eshazen/scope-clock/Data/3BP1 Base 1.gif

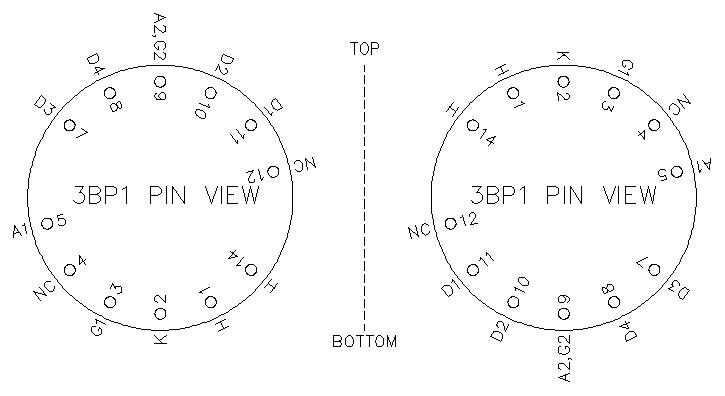
Data/3BP1 Base 1.gif
