eshazen/scope-clock/Data/3BP1 CRT 2.gif

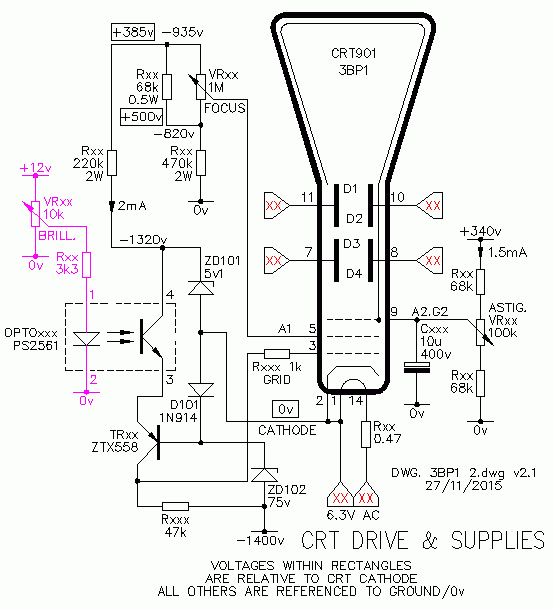
Data/3BP1 CRT 2.gif
