eshazen/scope-clock/Data/3BP1 NBTV Initial 9.gif

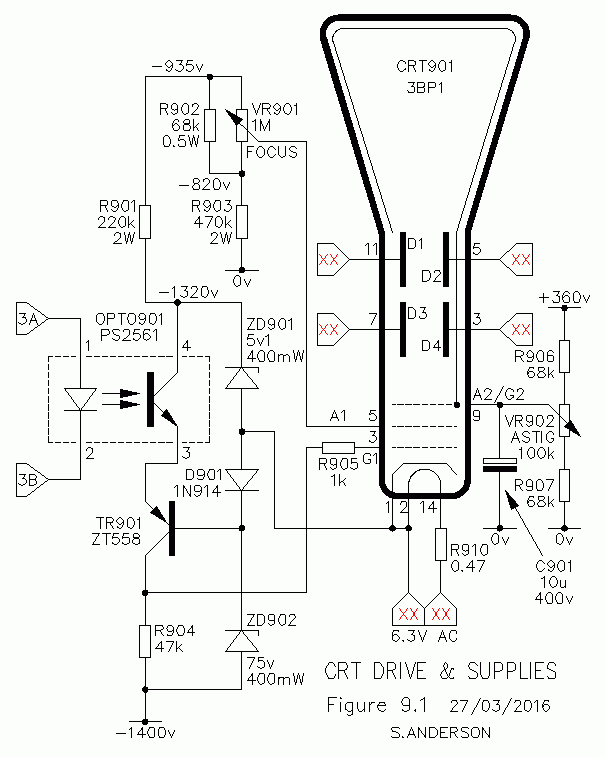
Data/3BP1 NBTV Initial 9.gif
