eshazen/scope-clock/Data/3BP1 PSU 2.gif

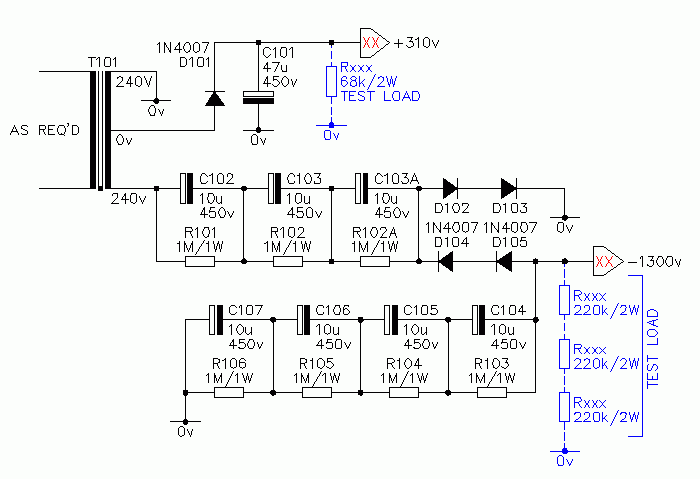
Data/3BP1 PSU 2.gif
