eshazen/scope-clock/Data/3BP1 PSU 3.gif

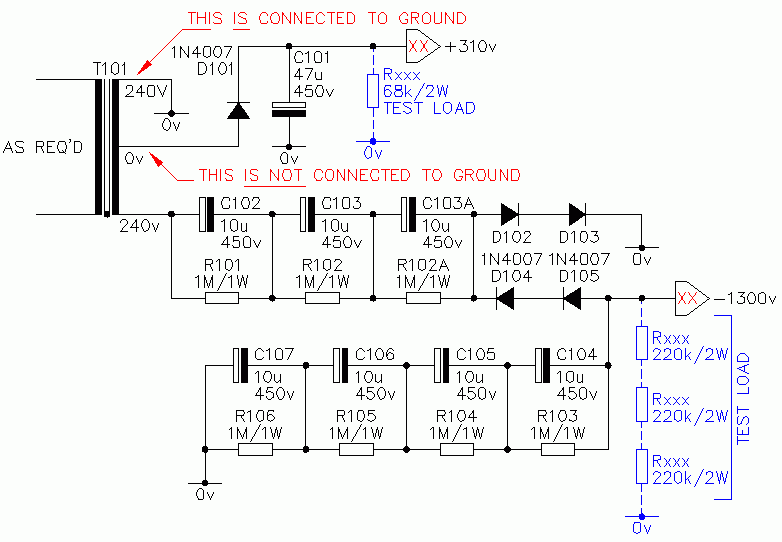
Data/3BP1 PSU 3.gif
