eshazen/scope-clock/Data/3BP1 PSU 4.gif

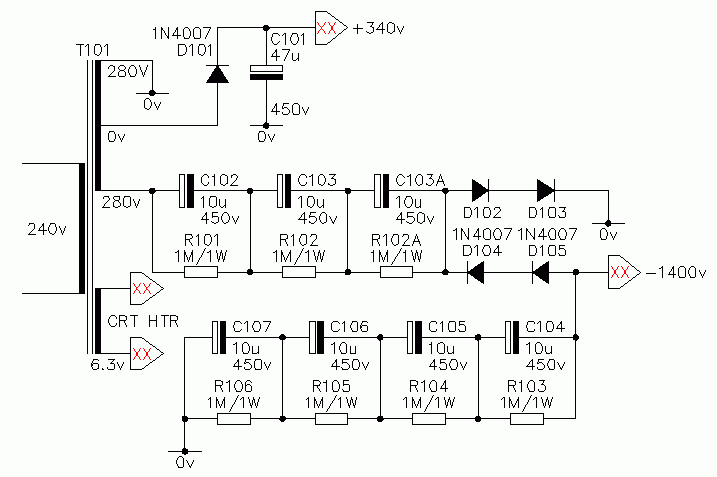
Data/3BP1 PSU 4.gif
