eshazen/scope-clock/Data/44a.gif

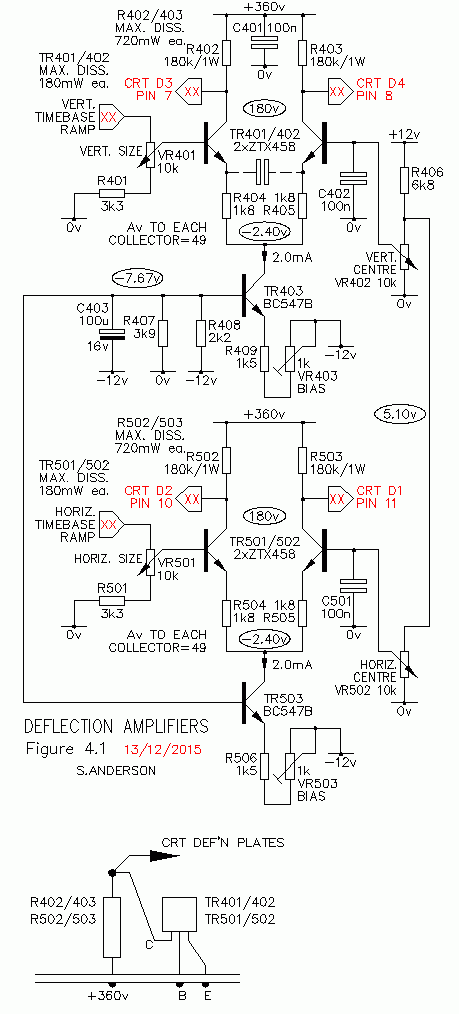
Data/44a.gif
