eshazen/scope-clock/hardware/psu/3D/e_0100.2041d007.step

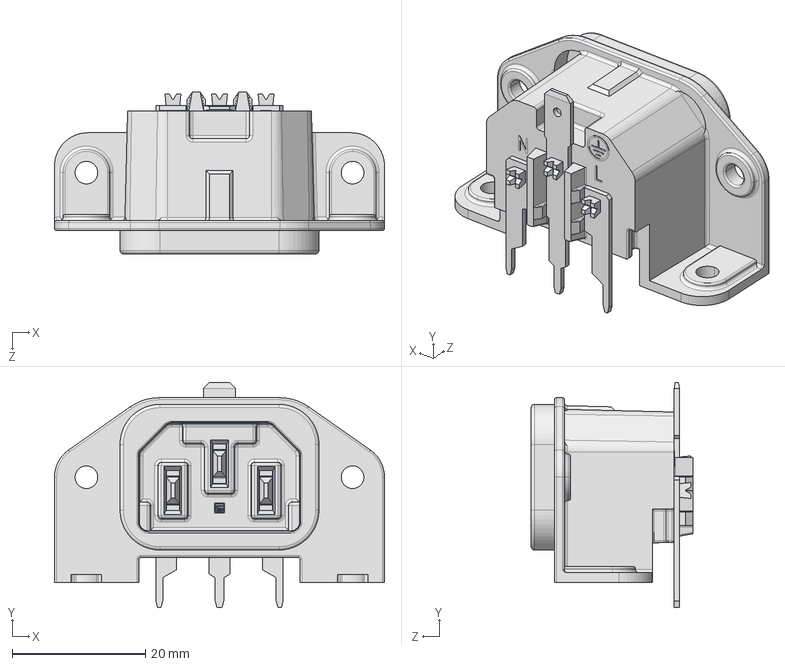
[picture p38: CAD file, 2022-12-22]
hardware/psu/3D/e_0100.2041d007.step
49.6 x 33.9 x 24.3 mm
