eshazen/scope-clock/hardware/case/back.dxf

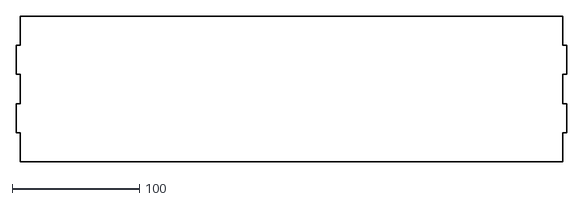
[picture p39: CAD file, 2024-02-05]
hardware/case/back.dxf
431.8 x 114.3
