eshazen/scope-clock/hardware/psu/3D/fuse_holder-Group001.step

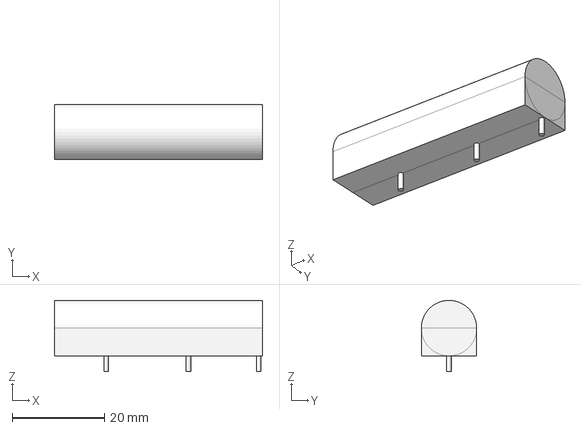
[picture p40: CAD file, 2022-12-22]
hardware/psu/3D/fuse_holder-Group001.step
45.0 x 12.0 x 15.4 mm
