eshazen/scope-clock/hardware/case/front.dxf

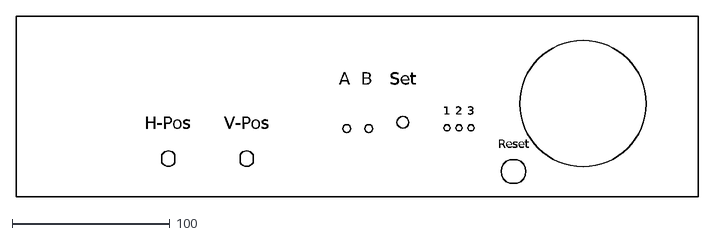
[picture p41: CAD file, 2024-02-05]
hardware/case/front.dxf
H-Pos
V-Pos
Set
A
B
1
2
3
Reset
