eshazen/scope-clock/hardware/case/deflection_amp-mech.dxf

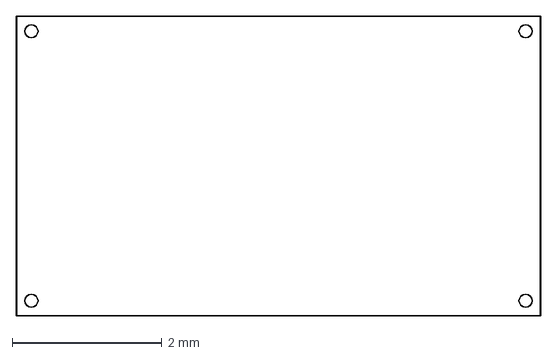
[picture p42: CAD file, 2024-02-02]
hardware/case/deflection_amp-mech.dxf
7.00 x 4.00 mm
