eshazen/scope-clock/hardware/case/psu-mech.dxf

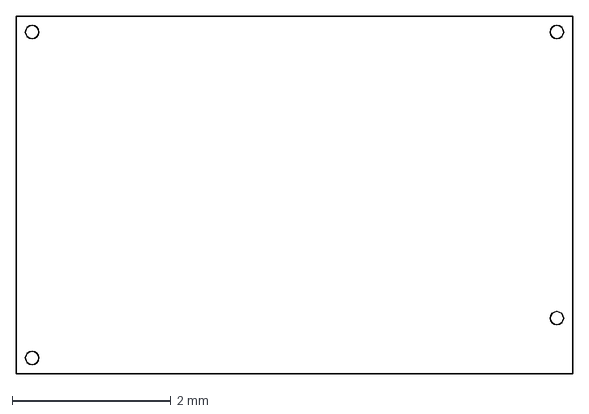
[picture p43: CAD file, 2024-02-02]
hardware/case/psu-mech.dxf
7.00 x 4.50 mm
