eshazen/scope-clock/hardware/case/base_plate_12x12.dxf

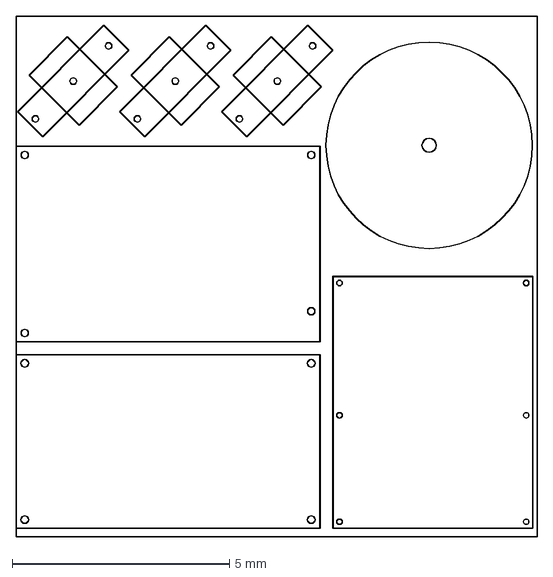
[picture p44: CAD file, 2024-02-02]
hardware/case/base_plate_12x12.dxf
12.0 x 12.0 mm
