eshazen/scope-clock/hardware/case/cpu-mech.dxf

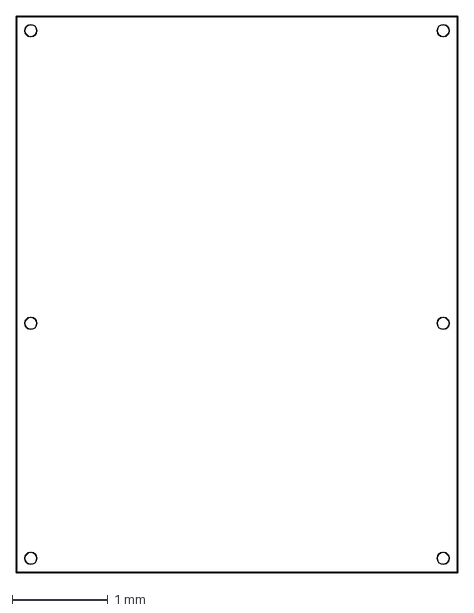
[picture p45: CAD file, 2024-02-02]
hardware/case/cpu-mech.dxf
4.60 x 5.80 mm
