eshazen/scope-clock/hardware/case/base_chassis.dxf

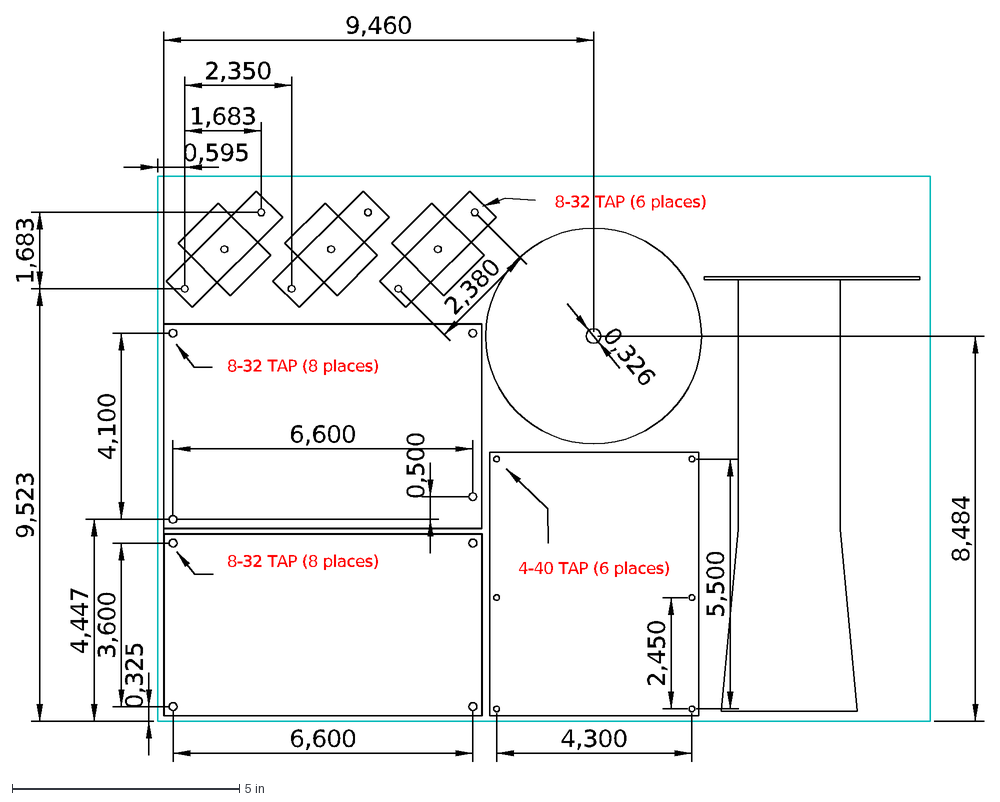
[picture p46: CAD file, 2024-02-02]
hardware/case/base_chassis.dxf
8-32 TAP (8 places)
4-40 TAP (6 places)
0,326
8-32 TAP (6 places)
0,325
4,447
9,523
1,683
0,595
2,350
3,600
4,100
6,600
4,300
5,500
2,450
9,460
8,484
2,380
0,500
