eshazen/scope-clock/hardware/case/base_plate.dxf

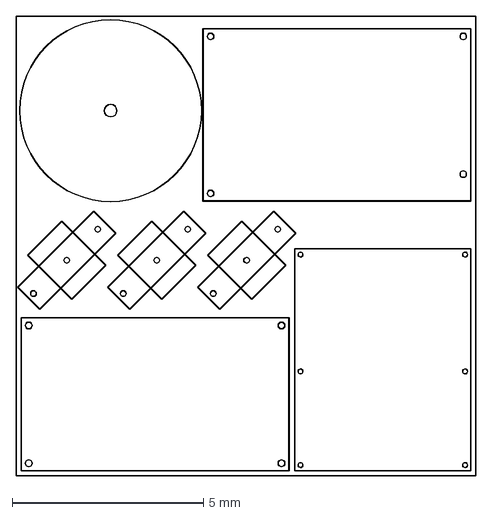
[picture p47: CAD file, 2024-02-02]
hardware/case/base_plate.dxf
12.0 x 12.0 mm
