eshazen/scope-clock/hardware/case/switch_bracket.stl

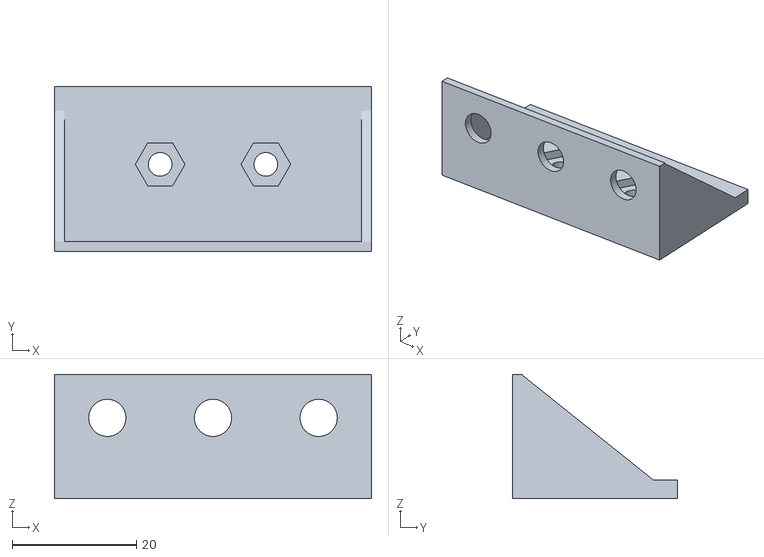
[picture p48: CAD file, 2022-12-28]
hardware/case/switch_bracket.stl
51.0 x 26.5 x 20.0
