eshazen/scope-clock/hardware/case/fuse_bracket.stl

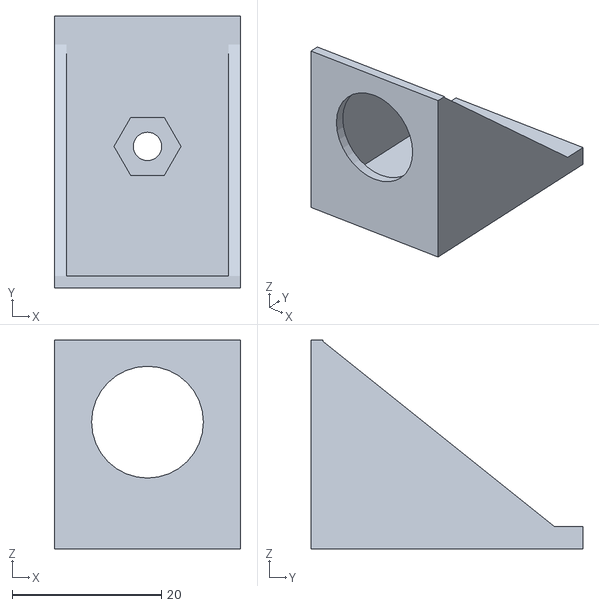
[picture p49: CAD file, 2022-12-28]
hardware/case/fuse_bracket.stl
25.0 x 36.5 x 28.0
