eshazen/scope-clock/hardware/case/hv_cw8.stl

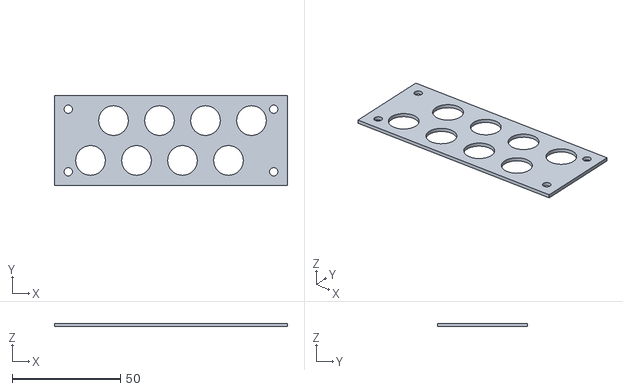
[picture p50: CAD file, 2022-12-22]
hardware/case/hv_cw8.stl
107.4 x 41.6 x 1.60
