eshazen/scope-clock/hardware/case/hv_cw.stl

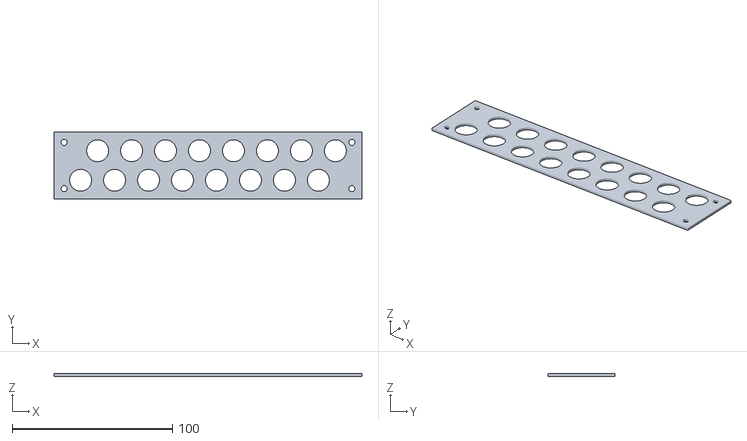
[picture p51: CAD file, 2022-12-22]
hardware/case/hv_cw.stl
192.2 x 41.6 x 1.60
