eshazen/scope-clock/hardware/case/hv_gen.stl

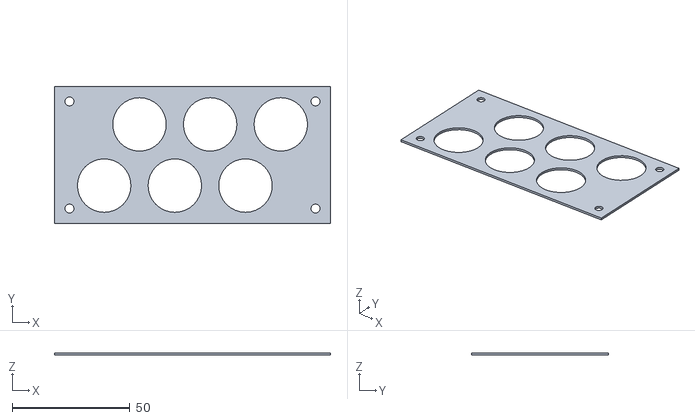
[picture p52: CAD file, 2022-12-16]
hardware/case/hv_gen.stl
117.2 x 58.2 x 1.00
