eshazen/scope-clock/hardware/deflection_amp/test.scad

import("deflection_amp.stl");
