eshazen/scope-clock/software/testio/list.asm

; 50 verteces
	DB 200
	DW 063cH, 08aaH
	DW 0650H, 08b4H
	DW 066eH, 08d2H
	DW 066eH, 0800H
	DW 06f0H, 08a0H
	DW 06f0H, 08aaH
	DW 06faH, 08beH
	DW 0704H, 08c8H
	DW 0718H, 08d2H
	DW 0740H, 08d2H
	DW 0754H, 08c8H
	DW 075eH, 08beH
	DW 0768H, 08aaH
	DW 0768H, 0896H
	DW 075eH, 0882H
	DW 074aH, 0864H
	DW 06e6H, 0800H
	DW 0772H, 0800H
	DW 07c2H, 088cH
	DW 07b8H, 0882H
	DW 07c2H, 0878H
	DW 07ccH, 0882H
	DW 07c2H, 088cH
	DW 07c2H, 0814H
	DW 07b8H, 080aH
	DW 07c2H, 0800H
	DW 07ccH, 080aH
	DW 07c2H, 0814H
	DW 0876H, 08d2H
	DW 0812H, 0846H
	DW 08a8H, 0846H
	DW 0876H, 08d2H
	DW 0876H, 0800H
	DW 0952H, 08d2H
	DW 08eeH, 08d2H
	DW 08e4H, 0878H
	DW 08eeH, 0882H
	DW 090cH, 088cH
	DW 092aH, 088cH
	DW 0948H, 0882H
	DW 095cH, 086eH
	DW 0966H, 0850H
	DW 0966H, 083cH
	DW 095cH, 081eH
	DW 0948H, 080aH
	DW 092aH, 0800H
	DW 090cH, 0800H
	DW 08eeH, 080aH
	DW 08e4H, 0814H
	DW 08daH, 0828H
	DB 0ffh
